JorgeLarach/Robotic-Arm/Documentation/Pictures/Dec_21_Pose.jpg

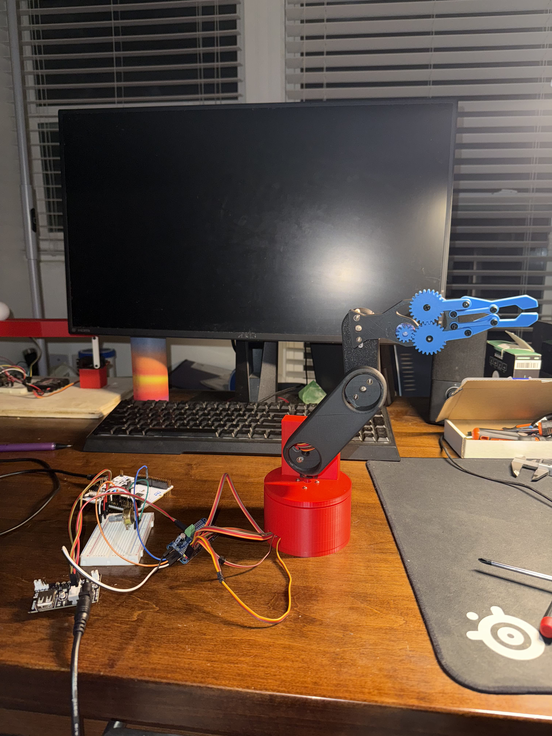
Documentation/Pictures/Dec_21_Pose.jpg
