JorgeLarach/Robotic-Arm/Documentation/3D Print STLs/Old STLs/Rotating Lid v1.0.stl

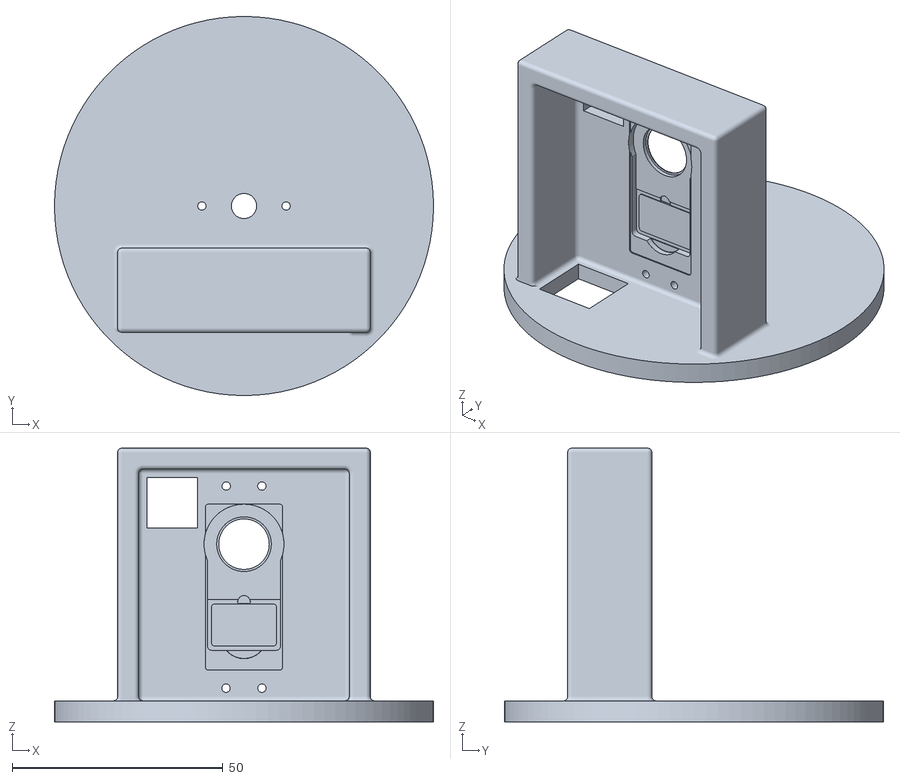
[picture p29: CAD file, 2025-12-21, an earlier design]
Documentation/3D Print STLs/Old STLs/Rotating Lid v1.0.stl
90.0 x 90.0 x 65.0
