JorgeLarach/Robotic-Arm/Documentation/3D Print STLs/Old STLs/Gripper Base v1.0.stl

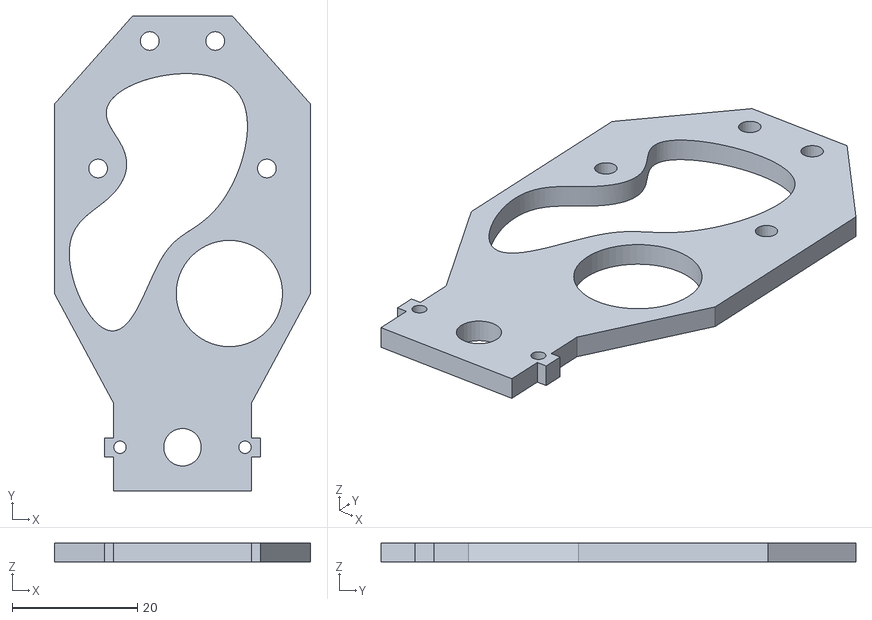
[picture p30: CAD file, 2025-12-21, an earlier design]
Documentation/3D Print STLs/Old STLs/Gripper Base v1.0.stl
41.0 x 76.0 x 3.00
