JorgeLarach/Robotic-Arm/Documentation/3D Print STLs/Electronics Box Lid v1.stl

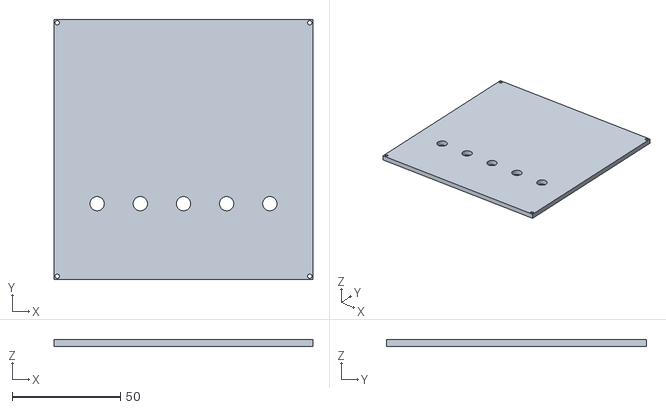
[picture p31: CAD file, 2026-01-06, an earlier design]
Documentation/3D Print STLs/Electronics Box Lid v1.stl
119.5 x 120.0 x 3.00
